migueldlr/medmate/cad/v2/servo base.SLDPRT

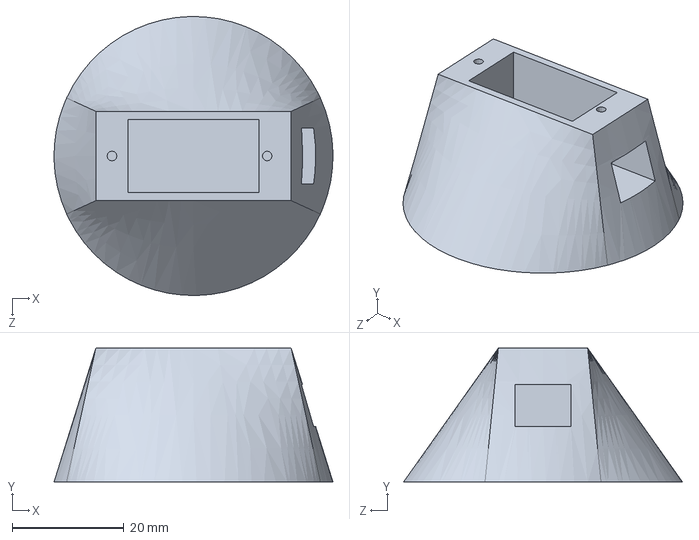
[picture p50: CAD file, 2020-10-04]
cad/v2/servo base.SLDPRT
50.0 x 24.0 x 50.0 mm
