migueldlr/medmate/cad/v2/semicircle for rotating part.SLDPRT

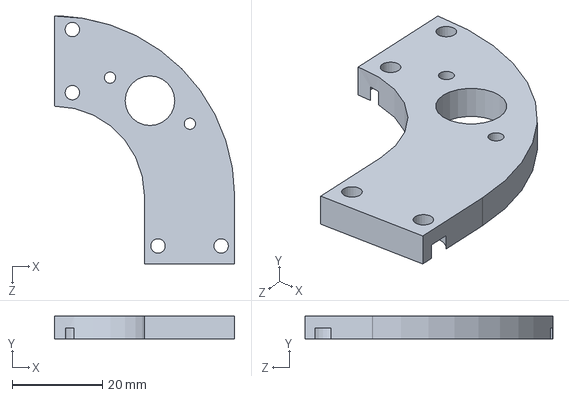
[picture p51: CAD file, 2020-10-04]
cad/v2/semicircle for rotating part.SLDPRT
40.0 x 5.00 x 55.0 mm
