migueldlr/medmate/cad/v2/4WaySurfaceMount.SLDPRT

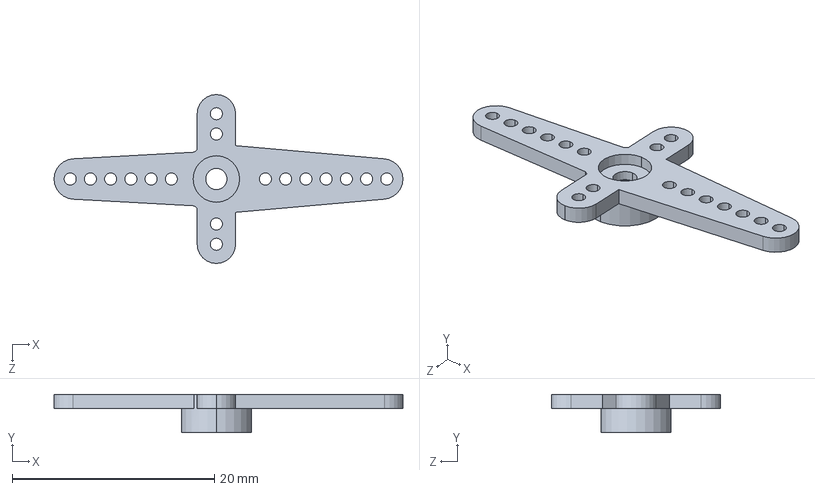
[picture p52: CAD file, 2020-10-04]
cad/v2/4WaySurfaceMount.SLDPRT
34.5 x 3.80 x 16.7 mm
