migueldlr/medmate/cad/v2/tube.SLDPRT

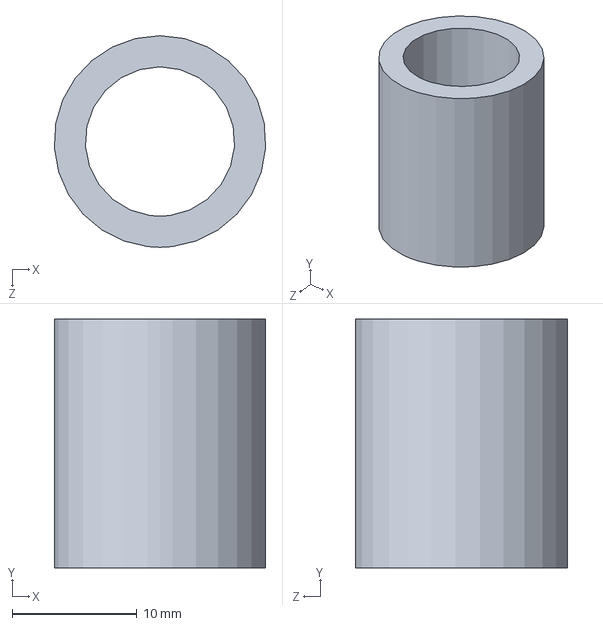
[picture p53: CAD file, 2020-10-04]
cad/v2/tube.SLDPRT
17.0 x 20.0 x 17.0 mm
