migueldlr/medmate/cad/v2/pill tube.SLDPRT

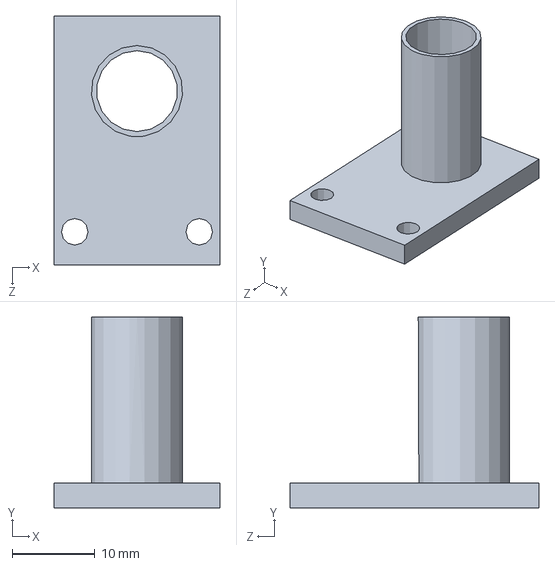
[picture p54: CAD file, 2020-10-04]
cad/v2/pill tube.SLDPRT
20.0 x 23.0 x 30.0 mm
