migueldlr/medmate/cad/v2/bottle holder v2.SLDPRT

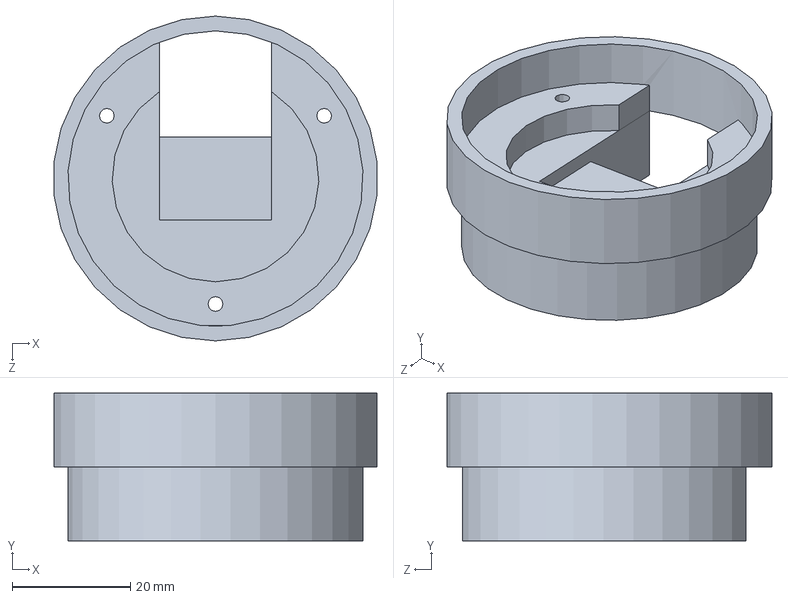
[picture p55: CAD file, 2020-10-04]
cad/v2/bottle holder v2.SLDPRT
54.7 x 25.0 x 55.0 mm
