migueldlr/medmate/cad/v2/frame.SLDPRT

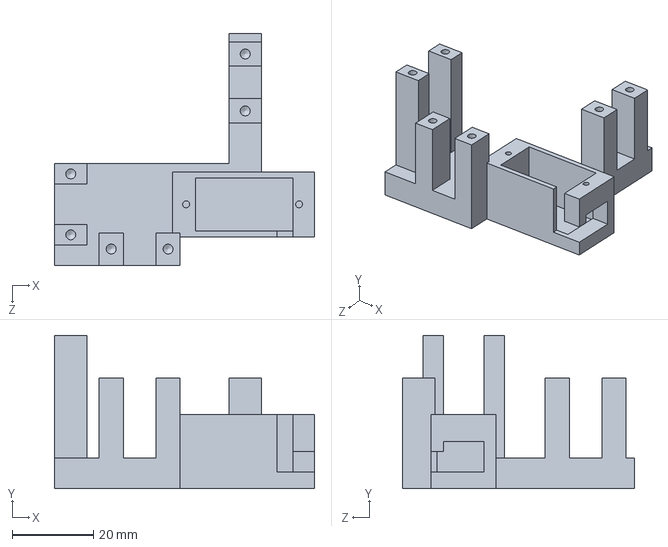
[picture p56: CAD file, 2020-10-04]
cad/v2/frame.SLDPRT
64.0 x 37.8 x 57.0 mm
