migueldlr/medmate/cad/v2/rotating cam.SLDPRT

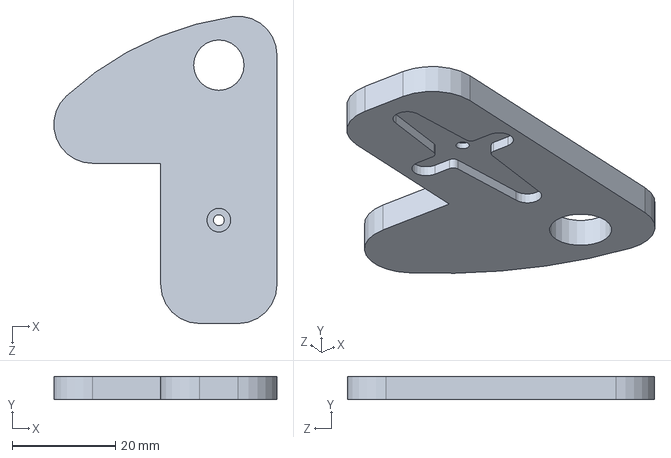
[picture p57: CAD file, 2020-10-04]
cad/v2/rotating cam.SLDPRT
43.2 x 4.50 x 59.4 mm
