migueldlr/medmate/device/Testing Scripts/FSR_Test2/FSR_Test2.ino

/* FSR simple testing sketch. 
 
Connect one end of FSR to power, the other end to Analog 0.
Then connect one end of a 10K resistor from Analog 0 to ground 
 
For more information see www.ladyada.net/learn/sensors/fsr.html */
 
int fsrPin = A0;     // the FSR and 10K pulldown are connected to a0
int fsrReading;     // the analog reading from the FSR resistor divider
 
void setup(void) {
  // We'll send debugging information via the Serial monitor
  Serial.begin(9600);   
}
 
void loop(void) {
  fsrReading = analogRead(fsrPin);  
 
  Serial.print("Analog reading = ");
  Serial.print(fsrReading);     // the raw analog reading
 
  // We'll have a few threshholds, qualitatively determined
  if (fsrReading < 10) {
    Serial.println(" - No pressure");
  } else if (fsrReading < 200) {
    Serial.println(" - Light touch");
  } else if (fsrReading < 500) {
    Serial.println(" - Light squeeze");
  } else if (fsrReading < 800) {
    Serial.println(" - Medium squeeze");
  } else {
    Serial.println(" - Big squeeze");
  }
  delay(1000);
} 
