migueldlr/medmate/device/Testing Scripts/TimeTest/TimeTest.ino

// Testing getting the exact time from an online web server

#include <WiFi.h>
#include "time.h"

const char* ssid     = "FiOS-3VPP9";
const char* password = "eat2359omni564bare";

const char* ntpServer = "pool.ntp.org";
const long  gmtOffset_sec = -18000; // Five hours behind in EST? have to check.
const int   daylightOffset_sec = 3600;

void setup(){
  Serial.begin(115200);

  // Connect to Wi-Fi
  Serial.print("Connecting to ");
  Serial.println(ssid);
  WiFi.begin(ssid, password);
  while (WiFi.status() != WL_CONNECTED) {
    delay(500);
    Serial.print(".");
  }
  Serial.println("");
  Serial.println("WiFi connected.");
  
  // Init and get the time
  configTime(gmtOffset_sec, daylightOffset_sec, ntpServer);
  printLocalTime();

  //disconnect WiFi as it's no longer needed
  WiFi.disconnect(true);
  WiFi.mode(WIFI_OFF);
}

void loop(){
  delay(1000);
  printLocalTime();
}

void printLocalTime(){ 
  struct tm timeinfo;
  if(!getLocalTime(&timeinfo)){
    Serial.println("Failed to obtain time");
    return;
  }
//  Serial.println(&timeinfo, "%A, %B %d %Y %H:%M:%S");
//  Serial.print("Day of week: ");
//  Serial.println(&timeinfo, "%A");
//  Serial.print("Month: ");
//  Serial.println(&timeinfo, "%B");
//  Serial.print("Day of Month: ");
//  Serial.println(&timeinfo, "%d");
//  Serial.print("Year: ");
//  Serial.println(&timeinfo, "%Y");
//  Serial.print("Hour: ");
//  Serial.println(&timeinfo, "%H");
//  Serial.print("Hour (12 hour format): ");
//  Serial.println(&timeinfo, "%I");
//  Serial.print("Minute: ");
//  Serial.println(&timeinfo, "%M");
//  Serial.print("Second: ");
//  Serial.println(&timeinfo, "%S");
//
//  Serial.println("Time variables");
//  char timeHour[3];
//  strftime(timeHour,3, "%H", &timeinfo);
//  Serial.println(timeHour);
  char timeWeekDay[30];
  strftime(timeWeekDay,30, "%A, %B %d %Y %H:%M:%S", &timeinfo);
  Serial.println(timeWeekDay);
  Serial.println();
}
