migueldlr/medmate/device/Testing Scripts/vcnl4010test/vcnl4010test.ino

#include <Wire.h>
#include "Adafruit_VCNL4010.h"

Adafruit_VCNL4010 vcnl;

void setup() {
  Serial.begin(115200);
  Serial.println("VCNL4010 test");

  if (! vcnl.begin()){
    Serial.println("Sensor not found :(");
    while (1);
  }
  Serial.println("Found VCNL4010");
}


void loop() {
   Serial.print("Ambient: "); Serial.println(vcnl.readAmbient());
   Serial.print("Proximity: "); Serial.println(vcnl.readProximity());
   delay(100);
}
